csu-grenoble/flatsat/Hardware/2U-PCB-TinyGS/2u-pcb-tinygs-01.png

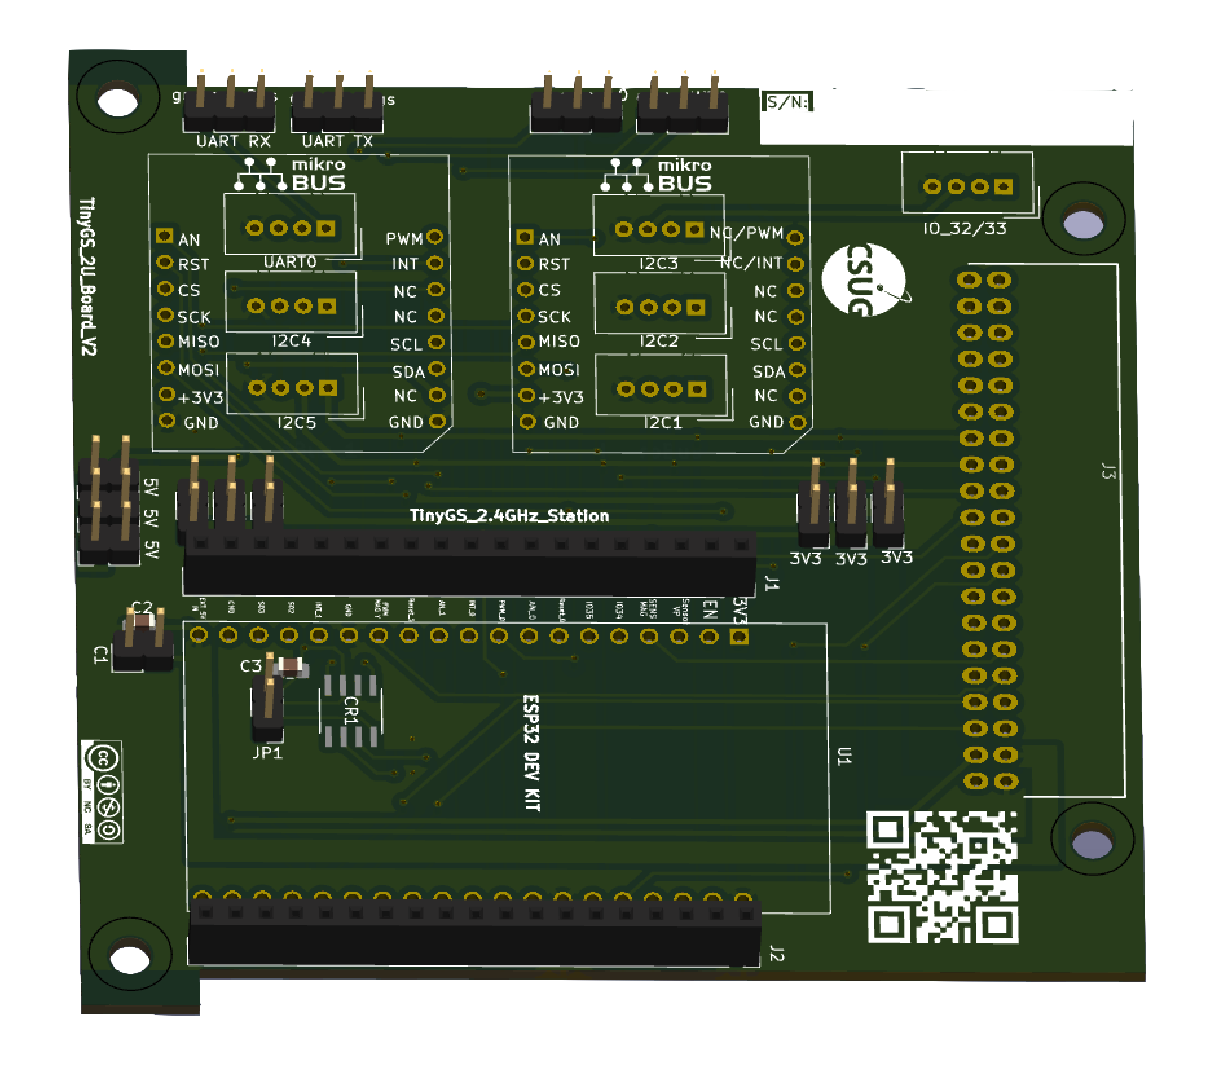
Hardware/2U-PCB-TinyGS/2u-pcb-tinygs-01.png
