csu-grenoble/flatsat/Hardware/Corecell_ESP32_Interconnection_module/Corecell_Nucleo32/Corecell_Nucleo32.png

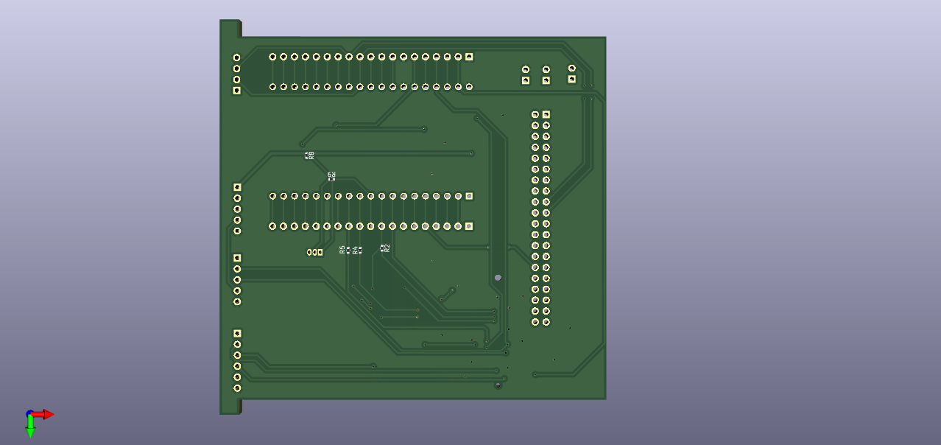
Hardware/Corecell_ESP32_Interconnection_module/Corecell_Nucleo32/Corecell_Nucleo32.png
