csu-grenoble/flatsat/media/inisat-01.jpg

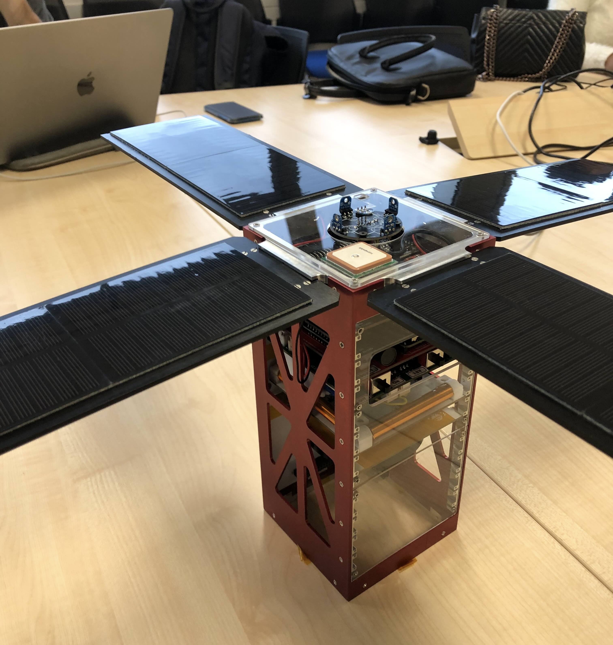
media/inisat-01.jpg
