csu-grenoble/flatsat/media/inisat-03.jpg

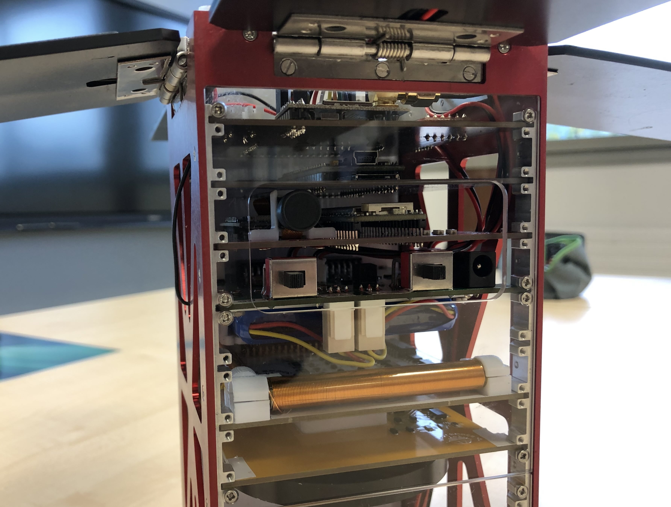
media/inisat-03.jpg
