csu-grenoble/flatsat/media/inisat-com-l432kc.jpg

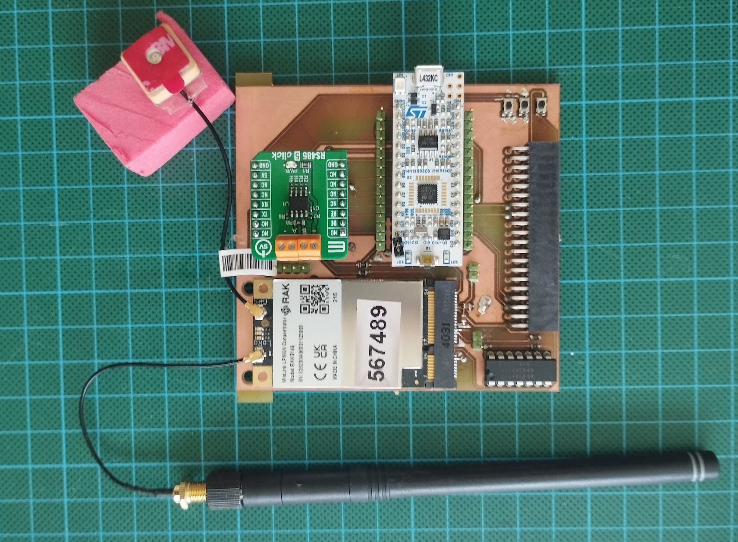
media/inisat-com-l432kc.jpg
