csu-grenoble/flatsat/media/inisat-obc+rak5146.png

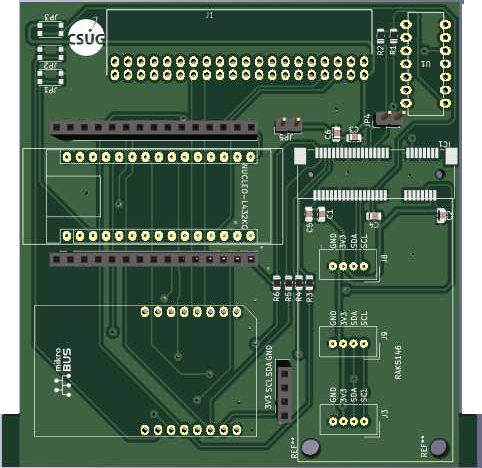
media/inisat-obc+rak5146.png
