csu-grenoble/flatsat/media/inisat-rak5146-proto-01.jpg

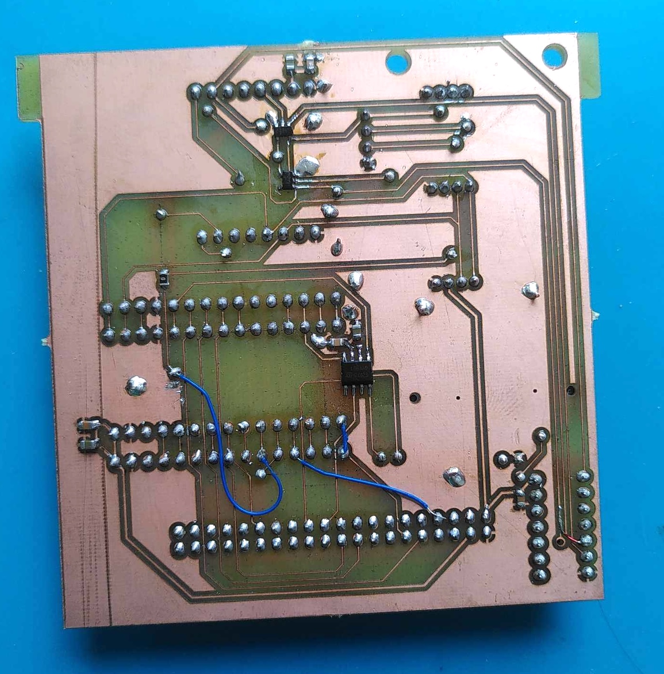
media/inisat-rak5146-proto-01.jpg
