csu-grenoble/flatsat/media/inisat-rak5146-proto-02.jpg

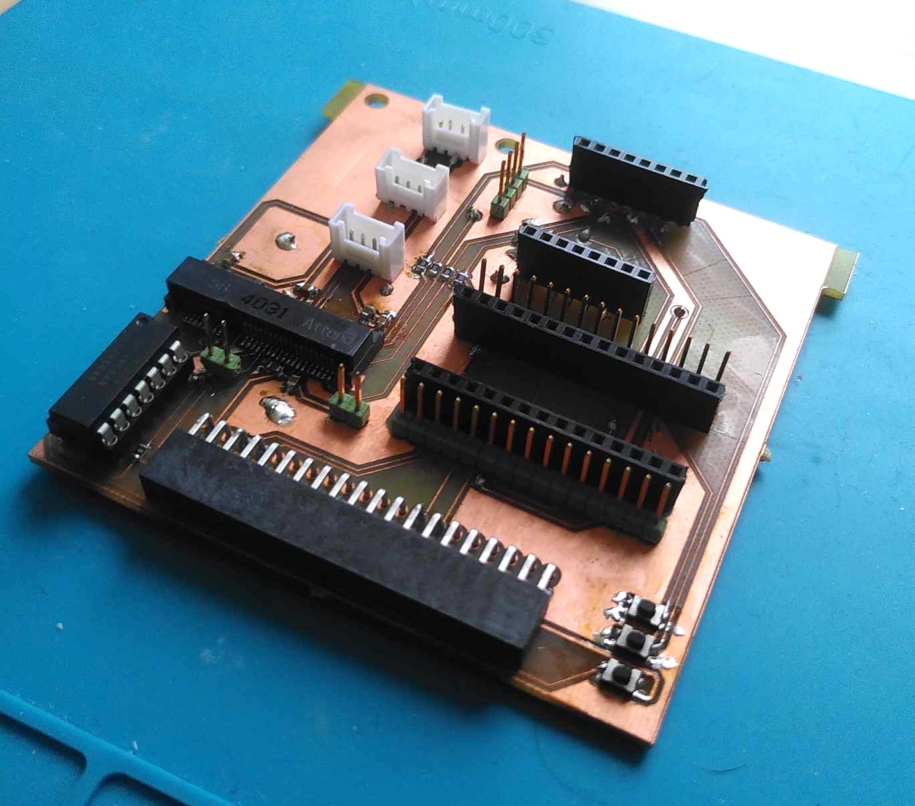
media/inisat-rak5146-proto-02.jpg
