csu-grenoble/flatsat/media/thingsat2-inisat-board.jpg

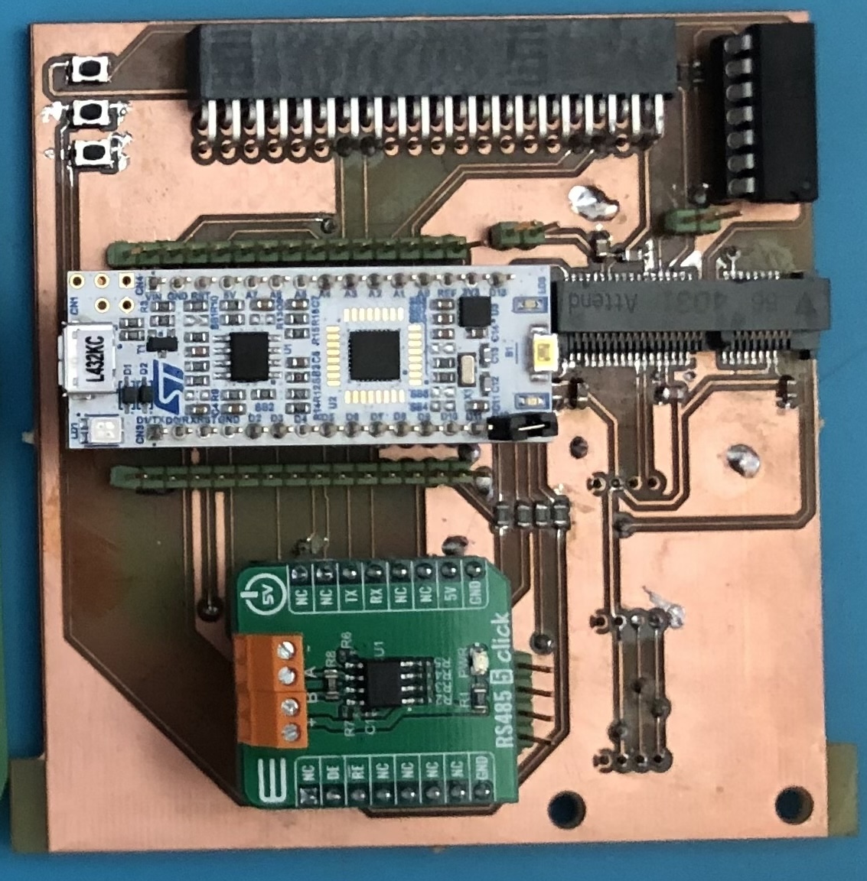
media/thingsat2-inisat-board.jpg
