csu-grenoble/flatsat/Software/cube/obc_l432kc/OBC_Software/Core/Inc/code_eleve.h

/*
 * code_eleve.h
 *
 *  Created on: Jun 29, 2023
 *      Author: lucas
 */

#ifndef CSUG_LIBRARY_INC_CODE_ELEVE_H_
#define CSUG_LIBRARY_INC_CODE_ELEVE_H_





#endif /* CSUG_LIBRARY_INC_CODE_ELEVE_H_ */
